sino-crdc/ZenS/Model_Physics/parameters/JY61加计陀螺仪角速度计1.jpg

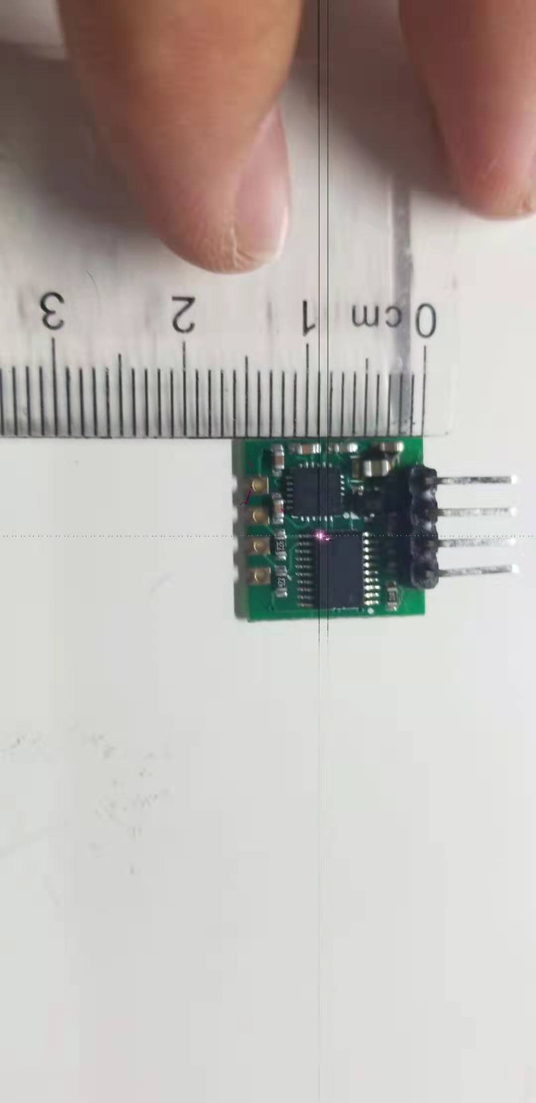
Model_Physics/parameters/JY61加计陀螺仪角速度计1.jpg
