sino-crdc/ZenS/Model_Physics/parameters/JY61加计陀螺仪角速度计2.jpg

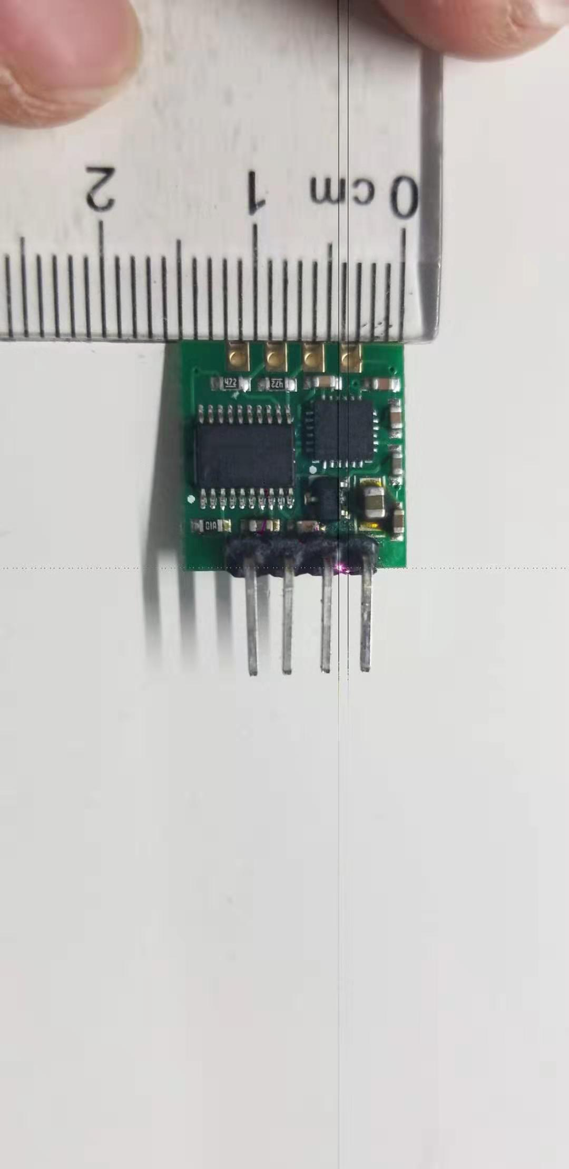
Model_Physics/parameters/JY61加计陀螺仪角速度计2.jpg
