sino-crdc/ZenS/Model_Physics/parameters/LED与红外发射管1.jpg

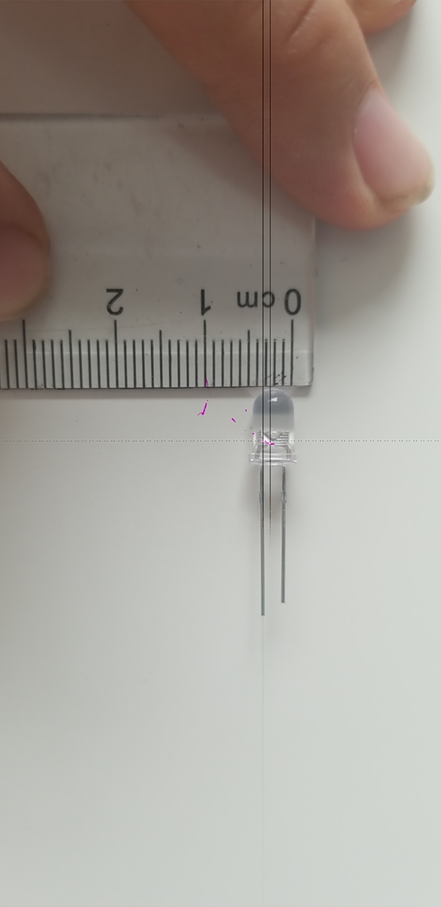
Model_Physics/parameters/LED与红外发射管1.jpg
