sino-crdc/ZenS/Model_Physics/parameters/LED与红外发射管2.jpg

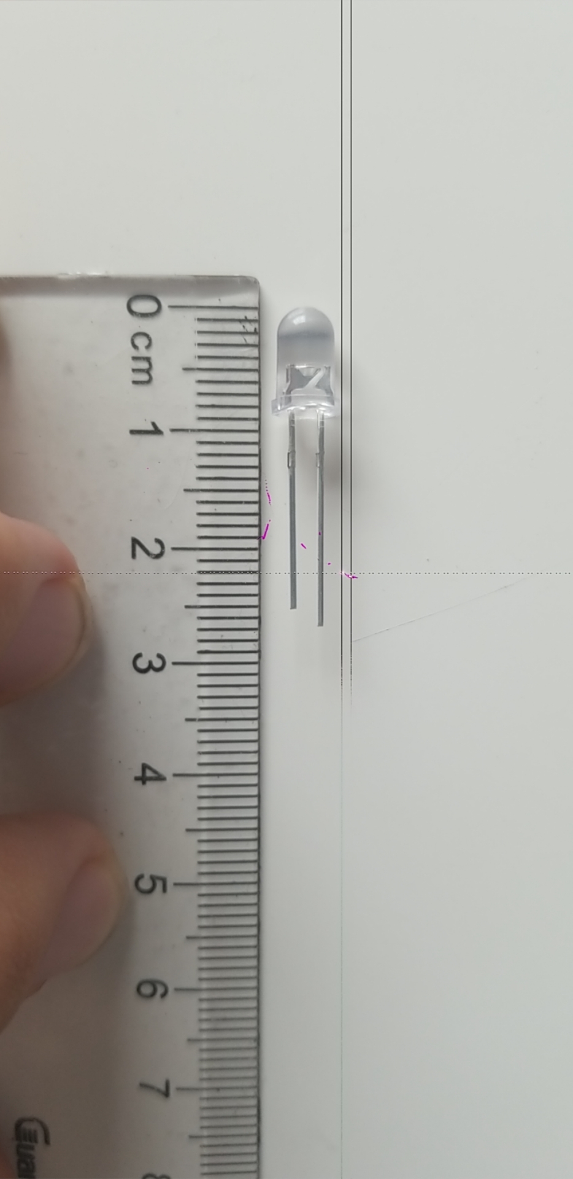
Model_Physics/parameters/LED与红外发射管2.jpg
