sino-crdc/ZenS/Model_Physics/parameters/SD卡读取器1.jpg

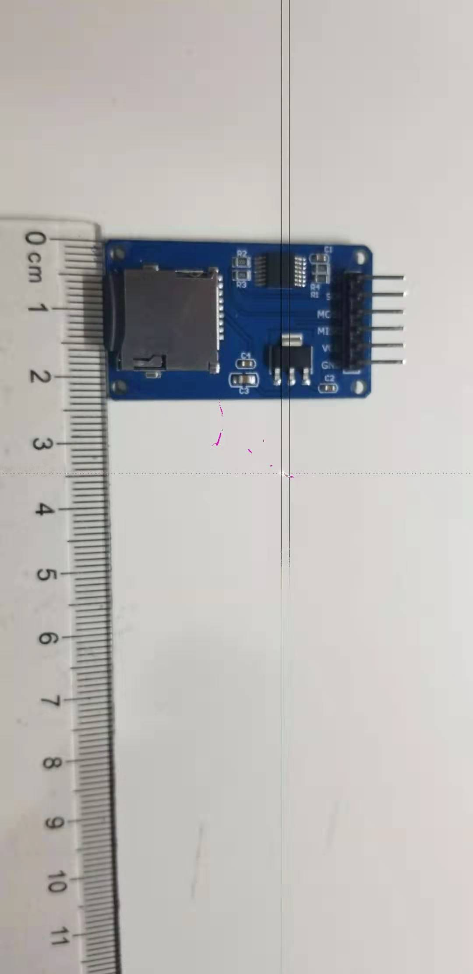
Model_Physics/parameters/SD卡读取器1.jpg
