sino-crdc/ZenS/Model_Physics/parameters/SD卡读取器2.jpg

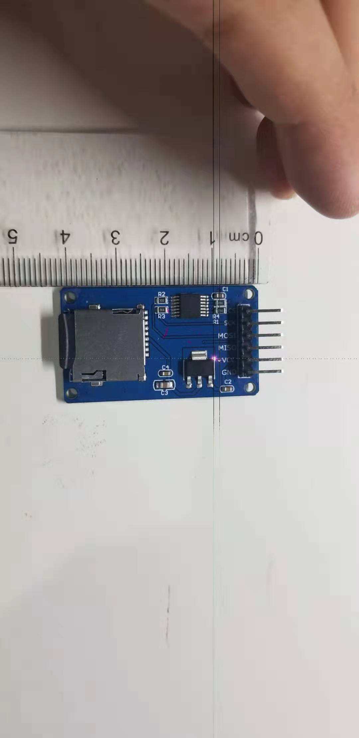
Model_Physics/parameters/SD卡读取器2.jpg
