sino-crdc/ZenS/Model_Physics/parameters/充放电一体化模块.jpg

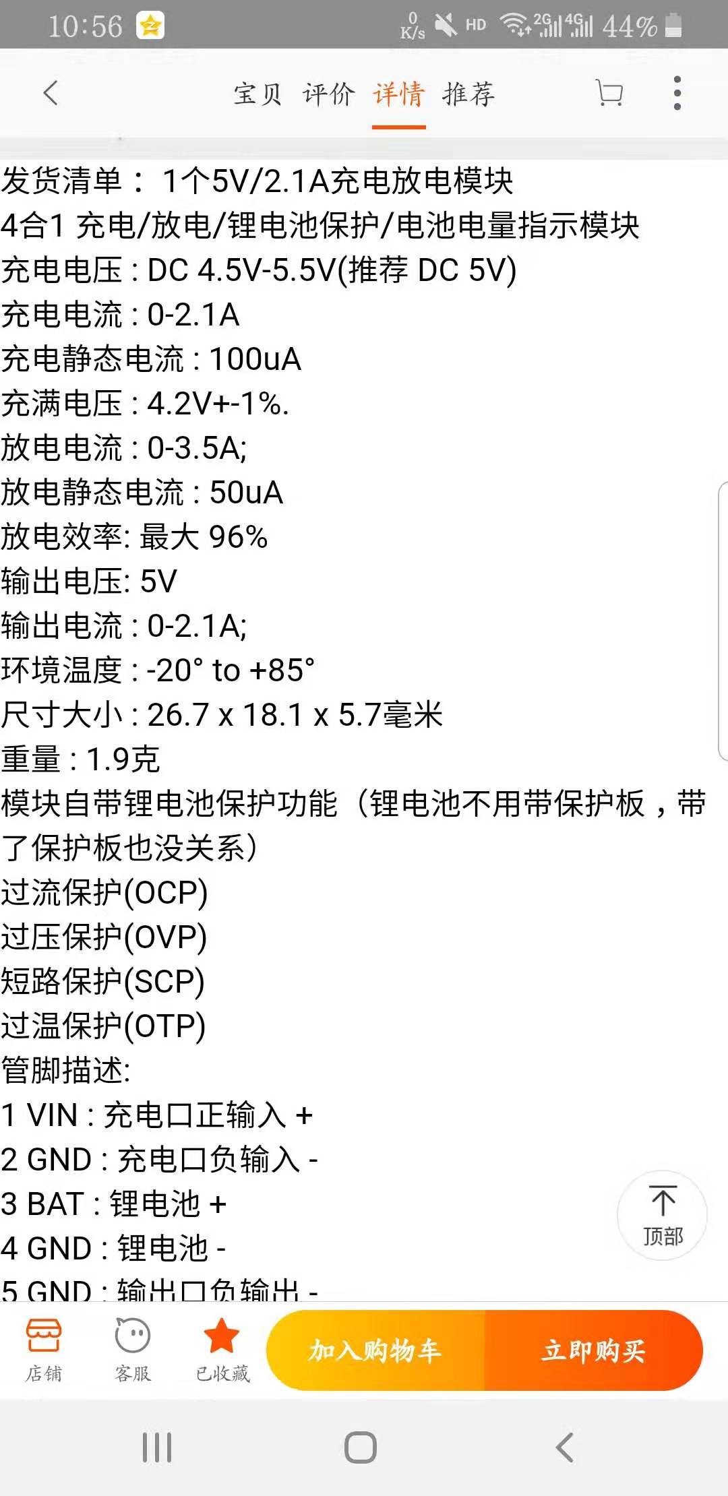
Model_Physics/parameters/充放电一体化模块.jpg
