sino-crdc/ZenS/Model_Physics/parameters/电池1.jpg

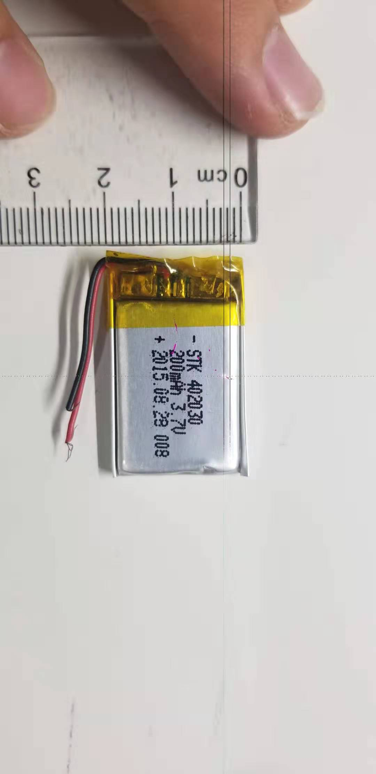
Model_Physics/parameters/电池1.jpg
