sino-crdc/ZenS/Model_Physics/parameters/电阻1.jpg

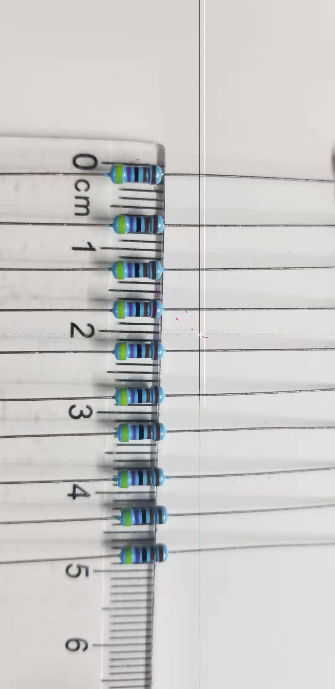
Model_Physics/parameters/电阻1.jpg
