sino-crdc/ZenS/Model_Physics/模型一  (1).jpg

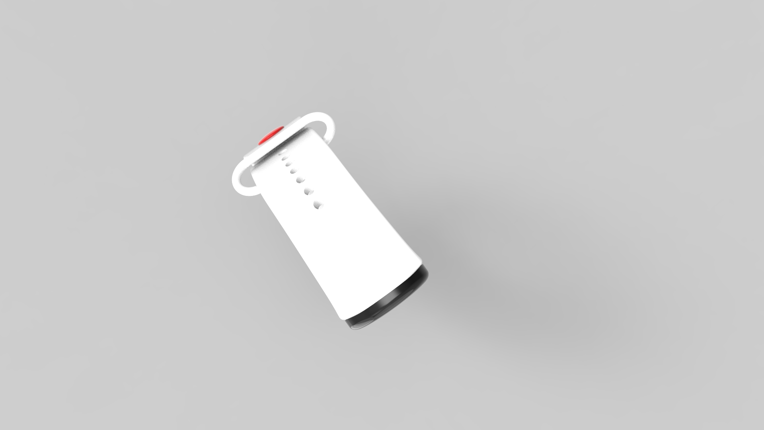
Model_Physics/模型一 (1).jpg
