sino-crdc/ZenS/Solution/ZenS_Whole.jpg

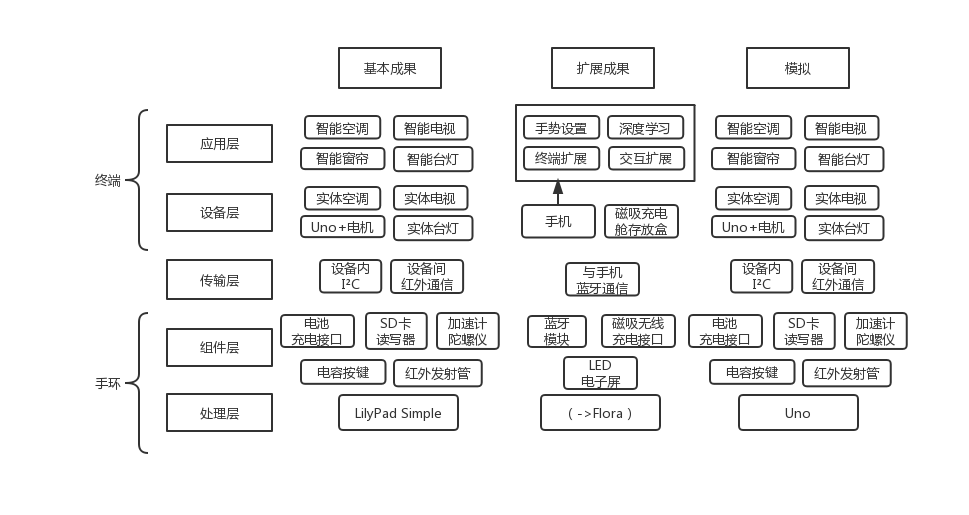
Solution/ZenS_Whole.jpg
