sino-crdc/ZenS/Test_Data/xa-ya-za的相互牵连关系.png

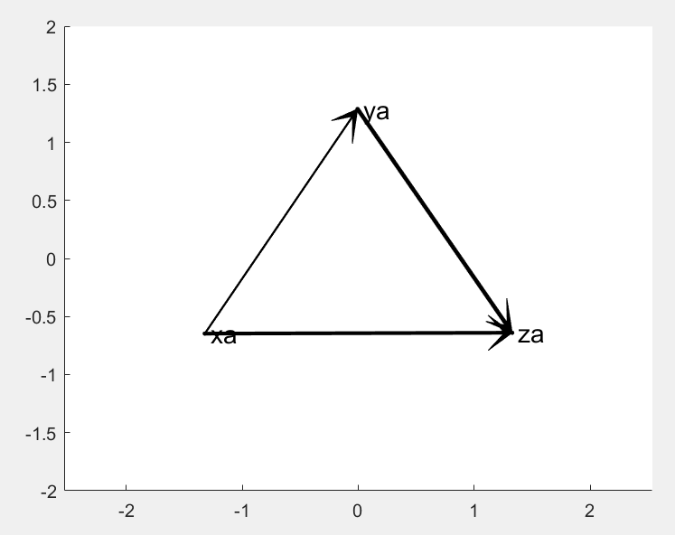
Test_Data/xa-ya-za的相互牵连关系.png
