sino-crdc/ZenS/Test_Data/xa与yaza的互信息.png

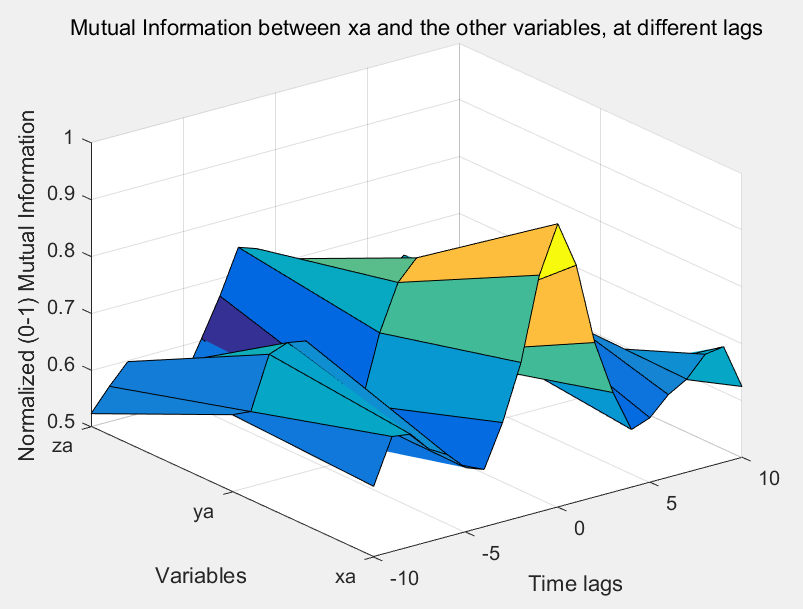
Test_Data/xa与yaza的互信息.png
