sino-crdc/ZenS/Test_Data/ya与xaza的互信息.png

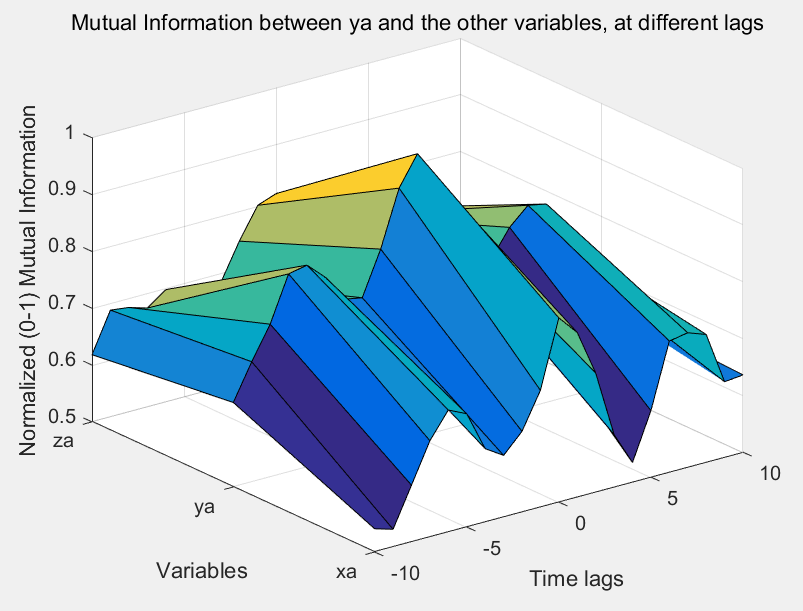
Test_Data/ya与xaza的互信息.png
