sino-crdc/ZenS/Test_Data/za与xaya的互信息.png

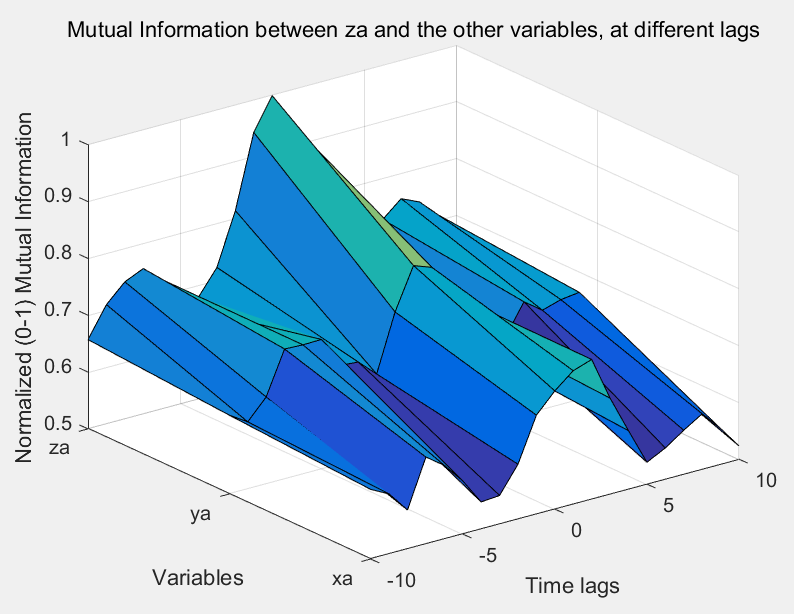
Test_Data/za与xaya的互信息.png
