sino-crdc/ZenS/Bracelet_Main/Bracelet_Main.ino

#if ARDUINO>=100
#include "Arduino.h"
#else
#include "WProgram.h"
#endif

#include "Setting.h"
#include <IRremote2.h>
#include <SD.h>
#include "Device.h"
#include "Gesture.h"
#include "Order.h"
#include "Controler.h"

Controler controler;

Device light = Device("Light", File(SdFile(), "light.txt"), LIGHT_ORDER_NUM);
Device air_conditioner = Device("AC", File(SdFile(), "AC.txt"), AC_ORDER_NUM);
Device television = Device("Tele", File(SdFile(), "Tele.txt"), TELE_ORDER_NUM);
Device curtain = Device("Curtain", File(SdFile(), "Curtain.txt"), CURTAIN_ORDER_NUM);

void setup() {
  Serial.begin(4800);
  controler.initial();
  Gesture::initial();
  pinMode(BUTTONA_PIN, INPUT);
  pinMode(BUTTONB_PIN, INPUT);
  pinMode(BUTTONC_PIN, INPUT);
  pinMode(BUTTOND_PIN, INPUT);
  pinMode(LEDA_PIN, OUTPUT);
  pinMode(LEDB_PIN, OUTPUT);
  pinMode(LEDC_PIN, OUTPUT);
  pinMode(LEDD_PIN, OUTPUT);
  pinMode(SD_PIN, OUTPUT);
}

void loop() {
  byte pin0 = controler.detect();//第一次按下的按键
  if (controler.isPressing()) {
    Device* device = controler.device();
    if (device == NULL) {
      return;
    }
    if (device != NULL) {
      Serial.println("device gotten.");
    }
    Gesture gesture = Gesture(device);
    Order* order = gesture.analyze(gesture.detect());
    if (order != NULL) {
      Serial.println("order is not NULL");
      if (!order->getIsQuantity()) {
        controler.send(order);
        Serial.println("order which is not Quantity finish");
      } else {
        unsigned long time0 = millis();//开始计时
        while (millis() - time0 < 10000L) { //小于十秒
          byte pin1 = controler.detect();
          Serial.println("pin1 detect: " + String(pin1));
          if (controler.isPressing() && pin1 == pin0) { //如果按键按下并且是相同设备
            Device* device_now = controler.device();
            Gesture gesture0 = Gesture(device_now);
            //            do {
            gesture0.quantity_detect(order);//包含命令发送
            //            } while ( controler.isPressing() && pin1 == pin0); //如果按键按下并且是相同设备
            //Device派生类成员变量的动态存储撤销
            device_now->three_clear();
            Serial.println("order which is Quantity send finish");
            break;
          }
        }
      }
    }
    controler.terminate();
  }
}
