sino-crdc/ZenS/Bracelet_Main/Gest_Data.h

#ifndef Gest_Data_H
#define Gest_Data_H
#if defined(ARDUINO)&&ARDUINO>=100
#include "Arduino.h"
#else
#include "WProgram.h"
#endif

class Device;

class Gest_Data {
  public:
    String equation;
    Device *device;

    Gest_Data(String equation, Device* device);
    Gest_Data(){
      Gest_Data("", NULL);
    }
};
//todo 修改没有上传到 master
#endif
